dersimn/HB-RF-USB-STICK/docs/img/bottom.jpeg

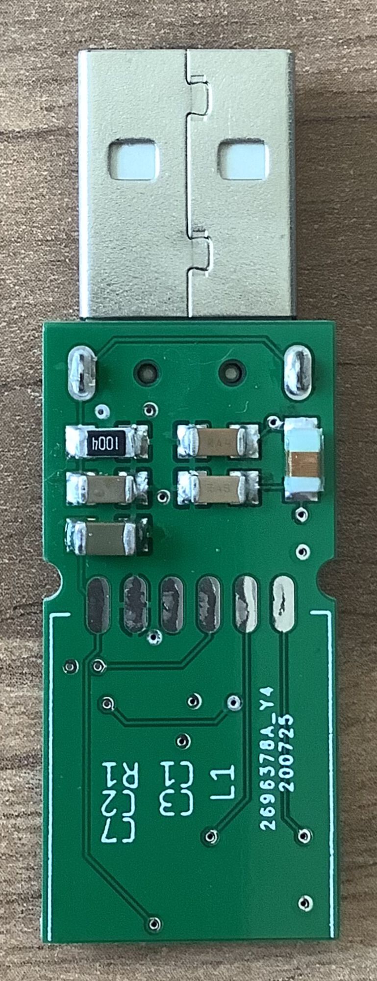
docs/img/bottom.jpeg
