dersimn/HB-RF-USB-STICK/docs/img/top.jpeg

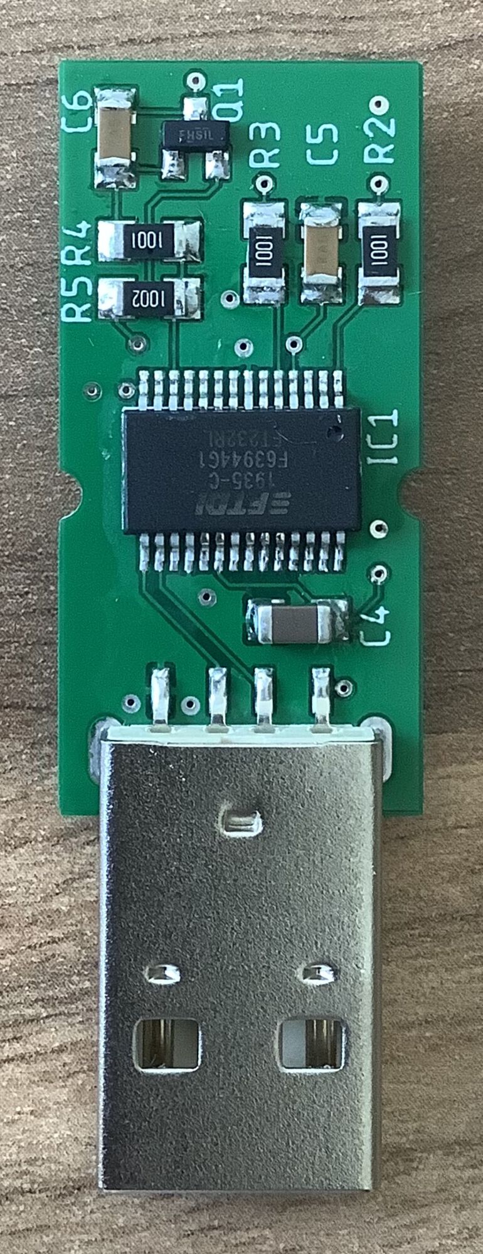
docs/img/top.jpeg
